issalig/led-clock/software/led_clock/number.h

/*
  file: number.h
  description: led masks for number-clock mode
  date: 08/11/2015
  author: Ismael Salvador
*/


#ifdef USE_EEPROM
#define _PROGMEM PROGMEM
#endif

//m_day_ten
//m_day_unit
//m_month
//m_hour
//m_min
//m_min_unit
//m_weather
//m_arrow
//m_pulse
//m_moon

const byte m_day_ten[] _PROGMEM ={
//0
B00100000,
B00000000,
B00000000,
B00000000,
B00000000,
B00000000,
B00000000,
B00000000,
//1
B10000000,
B00000000,
B00000000,
B00000000,
B00000000,
B00000000,
B00000000,
B00000000,
//2
B01000000,
B00000000,
B00000000,
B00000000,
B00000000,
B00000000,
B00000000,
B00000000,
//3
B00000000,
B00000000,
B00000000,
B10000000,
B00000000,
B00000000,
B00000000,
B00000000
};
const byte m_day_unit[] _PROGMEM ={
//0
B00100000,
B00000000,
B00000000,
B00000000,
B00000000,
B00000000,
B00000000,
B00000000,
//1
B00000000,
B10000000,
B00000000,
B00000000,
B00000000,
B00000000,
B00000000,
B00000000,
//2
B00000000,
B00000000,
B10000000,
B00000000,
B00000000,
B00000000,
B00000000,
B00000000,
//3
B00000000,
B00000000,
B00000000,
B10000000,
B00000000,
B00000000,
B00000000,
B00000000,
//4
B00000000,
B00000000,
B00000000,
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
};
const byte m_month[] _PROGMEM ={
//0
B00010000,
B00000000,
B00000000,
B00000000,
B00000000,
B00000000,
B00000000,
B00000000,
//1
B00001000,
B00000000,
B00000000,
B00000000,
B00000000,
B00000000,
B00000000,
B00000000,
//2
B00000100,
B00000000,
B00000000,
B00000000,
B00000000,
B00000000,
B00000000,
B00000000,
//3
B00000010,
B00000000,
B00000000,
B00000000,
B00000000,
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
B00010000,
//1
B00000000,
B00000000,
B00000000,
B00000000,
B00000000,
B00000000,
B00000000,
B00001000,
//2
B00000000,
B00000000,
B00000000,
B00000000,
B00000000,
B00000000,
B00000000,
B00000100,
//3
B00000000,
B00000000,
B00000000,
B00000000,
B00000000,
B00000000,
B00000000,
B00000010
};
