issalig/led-clock/software/led_clock/word.h

/*
  file: word.h
  description: masks for word mode
  date: 12/11/2015
  author: Ismael Salvador
*/


//MODIFY this file according to your word mask

//PROGMEM
//pgm_read_byte_near(charSet + k);

#ifdef USE_EEPROM
#define _PROGMEM PROGMEM
#endif

const  byte w_hour[] _PROGMEM ={    
  B00000000, //0 == 12
  B00000000,
  B00000000,
  B00000000,
  B00000000,
  B00001111,
  B00000000,
  B00000000,
  
  B11100000, //1
  B00000000,
  B00000000,
  B00000000,
  B00000000,
  B00000000,
  B00000000, 
  B00000000,
  
  B00000000, //2
  B00000000,
  B00000000,
  B00000000,
  B00000000,
  B00000000,
  B11100000, 
  B00000000,
  
  B00000000, //3
  B00000000,
  B00000000,
  B00000000,
  B00001111,
  B00000000,
  B00000000,
  B00000000,  
  
  B00000000, //4
  B00000111,
  B00000111,
  B00000000,
  B00000000,
  B00000000,
  B00000000,
  B00000000,
  
  B00000000, //5
  B00000000,
  B11111000,
  B00000000,
  B00000000,
  B00000000,
  B00000000,
  B00000000,
  
  B00000000, //6
  B00000000,
  B00000000,
  B11110000,
  B00000000,
  B00000000,
  B00000000,
  B00000000,
  
  B00011111, //7
  B00000000,
  B00000000,
  B00000000,
  B00000000,
  B00000000,
  B00000000,
  B00000000,
  
  B00000000, //8
  B00000000,
  B00000000,
  B00001111,
  B00000000,
  B00000000,
  B00000000,
  B00000000,
  
  B00000000, //9
  B11111000,
  B00000000,
  B00000000,
  B00000000,
  B00000000,
  B00000000,
  B00000000,
  
  B00000000, //10
  B00000000,
  B00000000,
  B00000000,
  B11110000,
  B00000000,
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
  B00000000,
  B00000000,
  B00000000,
  B00000000,
  B00000000,
  
  B00000000, //10
  B00000000,
  B00000000,
  B00000000,
  B11110000,
  B00000000,
  B00000000,
  B00000000,
  
  B00000000, //11
  B00000000,
  B00000000,
  B00000000,
  B00000000,
  B11110000,
  B00000000,
  B00000000
};
